cakemasterjedi/haloweb/src/settings.h

#pragma once
#include <stddef.h>
#include <stdint.h>
#include <string.h>

// Display modes. Keep in sync with MODES in web/index.html.
enum Mode : uint8_t {
    MODE_ROUNDEL = 0,  // static roundel
    MODE_SPIN,         // roundel with rotating quadrants
    MODE_STRIPES,      // M-style tri-colour stripes
    MODE_IMAGE,        // uploaded picture / animation
    MODE_TEXT,         // custom text in the middle
    MODE_M50,          // "50 Years of BMW M" badge
    MODE_M50_SPIN,     // ... with the quarters rotating
    MODE_COUNT
};

// Power behaviour.
enum PowerMode : uint8_t {
    POWER_NORMAL = 0,  // turns itself off after autoOffMin
    POWER_CAR_SHOW,    // stays on (optionally for showHours), own brightness
};

// Where the battery voltage comes from.
enum VoltSource : uint8_t {
    VOLT_NONE = 0,
    VOLT_BOARD,   // the board's LiPo connector (GPIO4 through a 1:3 divider)
    VOLT_INA219,  // INA219 module on the I2C connector (0x40), e.g. the car battery
};

static const uint8_t IMAGE_SLOTS = 10;
static const uint8_t DATE_RULES = 8;

// A design for certain days of the year, e.g. 1 Dec - 26 Dec: picture 4.
// The range can wrap over the new year. fromMonth 0 = unused.
struct DateRule {
    uint8_t fromMonth, fromDay, toMonth, toDay;
    uint8_t mode;  // Mode
    uint8_t slot;  // picture slot for MODE_IMAGE
};
static const uint32_t SETTINGS_VERSION = 11;
static const uint32_t CLASSIC_BLUE = 0x2C8BD6;  // default quarter colour

struct Settings {
    uint32_t version;

    // General
    uint8_t mode;
    uint8_t brightness;  // 5..100 %
    int8_t speed;        // -100..100, meaning depends on mode
    uint8_t imageSlot;   // 0..IMAGE_SLOTS-1
    int16_t angle;       // rotation offset in degrees, to line the emblem up on the car
    uint8_t panel;       // index into PANEL_TYPES (display_config.h)
    uint8_t startupAnim; // play the start-up animation at power-on
    uint8_t motionOff;   // don't use the motion sensor (was showIp in version 5)

    // Roundel (colours are 0xRRGGBB)
    uint32_t quadA;      // top-left + bottom-right quadrants
    uint32_t quadB;      // top-right + bottom-left quadrants
    uint32_t ring;       // outer ring
    uint32_t rim;        // silver rims
    uint32_t label;      // ring lettering
    char labelText[17];  // ring lettering, e.g. "BMW"
    uint8_t spacing;     // extra letter spacing on the ring (font units)

    // Stripes
    uint32_t stripe1, stripe2, stripe3, stripeBg;

    // Text
    uint32_t textBg, textFg;
    char text[33];  // '|' starts a new line

    // Power
    uint8_t powerMode;       // PowerMode
    uint16_t autoOffMin;     // normal mode: off after this many minutes (0 = never)
    uint8_t showHours;       // car show: off after this many hours (0 = until the battery says so)
    uint8_t showBrightness;  // car show brightness, %
    uint8_t lowVoltOn;       // shut down on low voltage
    uint16_t cutoffCV;       // low-voltage cutoff, centivolts
    uint8_t voltSource;      // VoltSource
    uint16_t voltCal;        // calibration factor x1000

    // Wi-Fi (not used by the renderer)
    char apSsid[33];
    char apPass[65];
    char staSsid[33];
    char staPass[65];

    // Version 7. Added at the end so version 5/6 settings load as a prefix.
    uint32_t cycleItems;      // auto-cycle: bit m = mode m (not MODE_IMAGE), bit 8+n = picture slot n
    uint16_t cycleSec;        // seconds per design, 0 = off
    uint16_t animSpeed;       // uploaded animations, % of normal speed (25..300)
    uint8_t bootSlot;         // start-up: 0 = built-in animation, n = picture slot n-1
    uint8_t fades;            // crossfade between designs
    uint8_t autoDim;          // dim at night by the clock
    uint8_t nightBrightness;  // %
    uint16_t nightFrom;       // night starts, minutes after midnight (local)
    uint16_t nightTo;         // night ends
    int16_t tzMin;            // local time offset from UTC in minutes (from the phone)
    uint8_t motionReact;      // 0..100: how much acceleration speeds up the effects
    uint8_t doubleTap;        // double-tap the badge for the next design: 0 off, 1..3 sensitivity
    int16_t levelRef;         // motion sensor: tilt reading when upright, 0.1 degrees
    int8_t levelSign;         // motion sensor: +1/-1 turning direction, 0 = not set up

    // Version 8 (starts on a 4-byte boundary, where version 7 ended).
    alignas(4) uint8_t welcomeOn;  // play a welcome clip on a jolt after the car has been still
    uint8_t welcomeSlot;      // 0 = built-in animation, n = picture slot n-1
    uint8_t welcomeSens;      // jolt sensitivity 1 (firm) .. 3 (light)
    uint8_t restMin;          // screen off after parked this long (minutes), 0 = never
    DateRule rules[DATE_RULES];

    // Version 9.
    alignas(4) uint8_t unused9;  // was "display output on core 0" (tore the picture, didn't help)

    // Version 10.
    alignas(4) uint8_t driveOn;  // unused (was the driving design, removed)
    uint8_t driveMode;           // unused
    uint8_t driveSlot;           // unused

    // Version 11.
    // First-time set-up done: a new emblem starts with its own Wi-Fi name and
    // a random password (shown on its screen) and asks for a new password
    // before anything else can be changed.
    alignas(4) uint8_t setupDone;
};

// Size of the stored settings before versions 7 to 11.
static const size_t SETTINGS_V6_SIZE = offsetof(Settings, cycleItems);
static const size_t SETTINGS_V7_SIZE = offsetof(Settings, welcomeOn);
static const size_t SETTINGS_V8_SIZE = offsetof(Settings, unused9);
static const size_t SETTINGS_V9_SIZE = offsetof(Settings, driveOn);
static const size_t SETTINGS_V10_SIZE = offsetof(Settings, setupDone);

inline void settingsDefaults(Settings &s) {
    memset(&s, 0, sizeof(s));
    s.version = SETTINGS_VERSION;
    s.mode = MODE_ROUNDEL;
    s.brightness = 80;
    s.speed = 30;
    s.imageSlot = 0;
    s.angle = 0;
    s.panel = 0;
    s.startupAnim = 1;

    s.quadA = CLASSIC_BLUE;
    s.quadB = 0xFFFFFF;
    s.ring = 0x000000;
    s.rim = 0xB8BCC2;
    s.label = 0xFFFFFF;
    strcpy(s.labelText, "BMW");
    s.spacing = 12;

    s.stripe1 = 0x3FA9F5;
    s.stripe2 = 0x1B3D8F;
    s.stripe3 = 0xE22718;
    s.stripeBg = 0x16181B;

    s.textBg = 0x000000;
    s.textFg = 0xFFFFFF;
    strcpy(s.text, "M|POWER");

    s.powerMode = POWER_NORMAL;
    s.autoOffMin = 0;
    s.showHours = 0;
    s.showBrightness = 60;
    s.lowVoltOn = 0;
    s.cutoffCV = 1200;  // 12.00 V (car battery via INA219)
    s.voltSource = VOLT_NONE;
#ifdef KIT_DEFAULTS
    // Ready-to-ship kit (INA219 pre-wired in the power module): battery
    // protection on from the first start. Auto-off stays off (see above):
    // on an always-on fuse it would leave the emblem off until BOOT is pressed.
    s.voltSource = VOLT_INA219;
    s.lowVoltOn = 1;
    s.cutoffCV = 1220;  // 12.20 V
#endif
    s.voltCal = 1000;

    s.cycleItems = (1u << MODE_ROUNDEL) | (1u << MODE_SPIN);
    s.cycleSec = 0;
    s.animSpeed = 100;
    s.bootSlot = 0;
    s.fades = 1;
    s.autoDim = 0;
    s.nightBrightness = 35;
    s.nightFrom = 19 * 60;
    s.nightTo = 7 * 60;
    s.tzMin = 0;
    s.motionReact = 0;
    s.doubleTap = 0;
    s.levelRef = 0;
    s.levelSign = 0;

    s.welcomeOn = 0;
    s.welcomeSlot = 0;
    s.welcomeSens = 2;
    s.restMin = 0;

    s.driveOn = 0;
    s.driveMode = MODE_SPIN;
    s.driveSlot = 0;

    strcpy(s.apSsid, "BMW-Emblem");
    strcpy(s.apPass, "emblem123");
}
